LennartEd/Arduino-pro-micro-macro-pad-5x5/IMG_20230509_133125.jpg

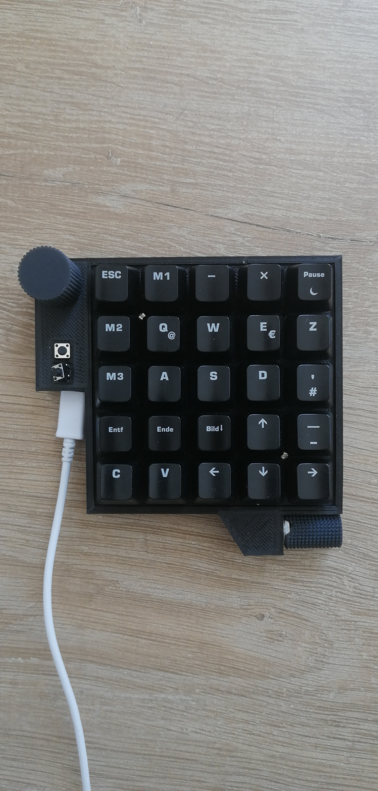
IMG_20230509_133125.jpg
